shapoco/pico-env-mon/src/images.cpp

#include "msb1stimage.hpp"

const uint8_t img_digit16_data[] = {
    116, 0, 16, 0,
    0xe1, 0xfc, 0x7f, 0x3f, 0xcf, 0xc7, 0xe0, 0x1c, 0x7c, 0x00, 0xf3, 0xfc, 0xff, 0xff, 0x80, 0xc0, 
    0xf8, 0x7c, 0x0f, 0x03, 0xc7, 0xe0, 0x1c, 0x7c, 0x00, 0xc0, 0xf0, 0x3f, 0xff, 0x80, 0x80, 0x70, 
    0x78, 0x06, 0x01, 0x87, 0xe0, 0x1c, 0x7c, 0x00, 0x80, 0x60, 0x1f, 0xff, 0x80, 0x8c, 0x70, 0x70, 
    0xc0, 0x30, 0x8f, 0xe3, 0xf8, 0xfc, 0x78, 0x0c, 0x23, 0x0f, 0xff, 0x80, 0x0c, 0x34, 0x79, 0xe2, 
    0x78, 0x8f, 0xc7, 0xf8, 0xfc, 0x70, 0x1e, 0x07, 0x8f, 0xff, 0x10, 0x1e, 0x3c, 0x7f, 0xe3, 0xf0, 
    0x08, 0xc4, 0xf8, 0x3f, 0xf1, 0x0c, 0x07, 0x8f, 0xff, 0x10, 0x1e, 0x3c, 0x7f, 0xc3, 0x81, 0x18, 
    0xc0, 0x38, 0x0f, 0xf1, 0x80, 0x47, 0x8f, 0xff, 0x10, 0x1e, 0x3c, 0x7f, 0x87, 0x83, 0x18, 0xc0, 
    0x10, 0x07, 0xe1, 0xc0, 0xe3, 0x0f, 0x03, 0x10, 0x1e, 0x3c, 0x7f, 0x0f, 0x81, 0x18, 0xc7, 0x00, 
    0xc7, 0xe3, 0x80, 0x60, 0x0f, 0x02, 0x30, 0x1e, 0x3c, 0x7e, 0x1f, 0xf0, 0x00, 0x3f, 0x81, 0xe3, 
    0xe3, 0x0c, 0x30, 0x1f, 0x02, 0x30, 0x1e, 0x3c, 0x7c, 0x3f, 0xf8, 0x00, 0x3f, 0x81, 0xe3, 0xe3, 
    0x1e, 0x3c, 0x1f, 0xfe, 0x30, 0x0c, 0x3c, 0x78, 0x7e, 0x78, 0x00, 0x27, 0x81, 0xe3, 0xc3, 0x1e, 
    0x3f, 0x1f, 0xfe, 0x30, 0x8c, 0x7c, 0x78, 0xfc, 0x30, 0xf8, 0xc3, 0x10, 0xc7, 0xc7, 0x0c, 0x3f, 
    0x19, 0xfc, 0x70, 0x80, 0x7c, 0x70, 0x02, 0x01, 0xf8, 0xe0, 0x18, 0x07, 0xc7, 0x80, 0x7e, 0x30, 
    0xfc, 0x70, 0xc0, 0xfc, 0x70, 0x03, 0x03, 0xf8, 0xf0, 0x3c, 0x0f, 0xc7, 0xc0, 0xfe, 0x30, 0xfc, 
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
    9, 0, 16, 0,
    0x55, 0x00, 0x55, 0x00, 0xf7, 0x80, 0xe3, 0x80, 0xc1, 0x80, 0x80, 0x80, 0xe3, 0x80, 0xe3, 0x80, 
    0xe3, 0x80, 0xe3, 0x80, 0x80, 0x80, 0xc1, 0x80, 0xe3, 0x80, 0xf7, 0x80, 0x55, 0x00, 0x55, 0x00, 
};

Msb1stImage img_step((uint8_t*)img_step_data);
