shapoco/pico-env-mon/src/images.hpp

#ifndef IMAGES_HPP
#define IMAGES_HPP

#include "msb1stimage.hpp"
extern Msb1stImage img_digit16;
extern Msb1stImage img_digit32;
extern Msb1stImage img_degc;
extern Msb1stImage img_percent;
extern Msb1stImage img_hpa;
extern Msb1stImage img_ppm;
extern Msb1stImage img_step;
 
#endif
